th31dk/HexHub/assets/watermark.png

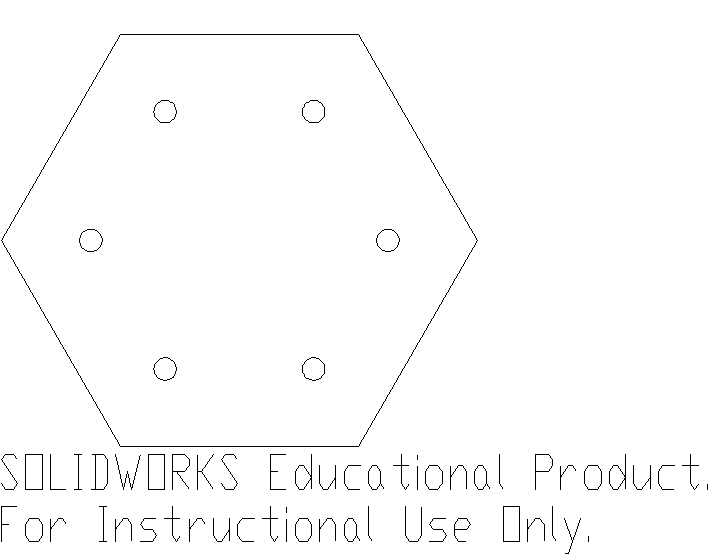
assets/watermark.png
